sparkfun/SparkFun_Simultaneous_RFID_Reader_M7E/docs/assets/img/Simultaneous-RFID-Reader_M7E-Power.jpg

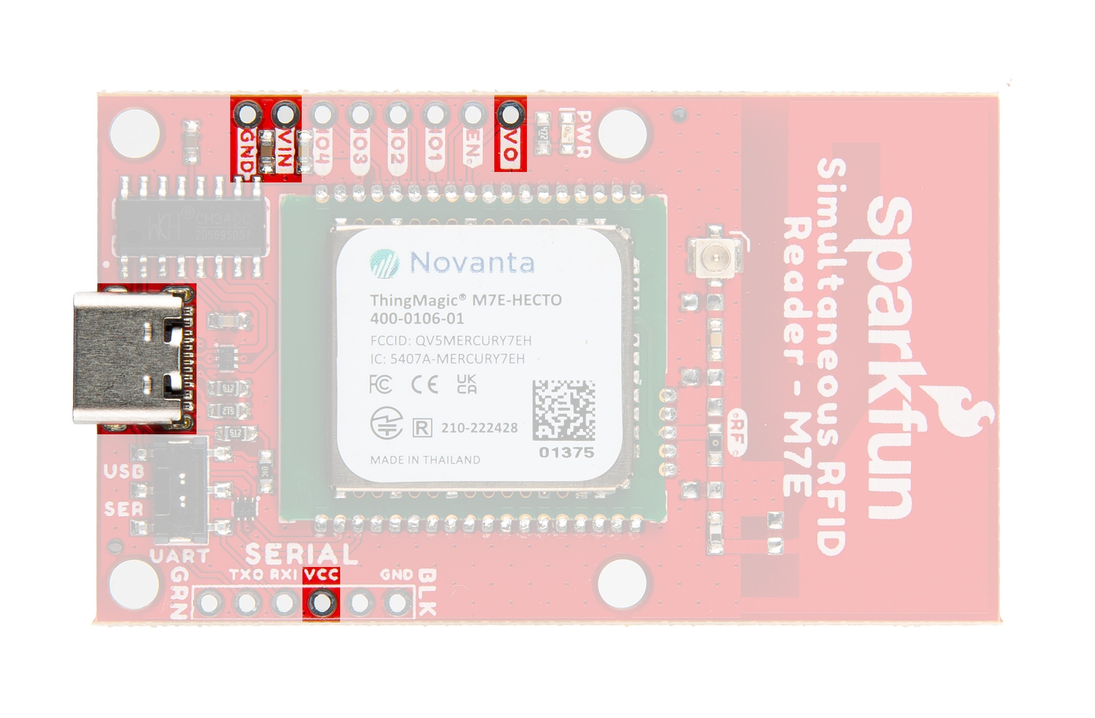
docs/assets/img/Simultaneous-RFID-Reader_M7E-Power.jpg
