sparkfun/SparkFun_Simultaneous_RFID_Reader_M7E/docs/assets/img/Simultaneous-RFID-Reader_M7E-Switch.jpg

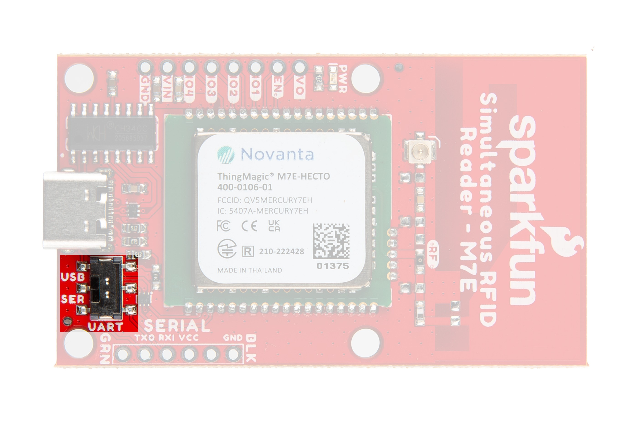
docs/assets/img/Simultaneous-RFID-Reader_M7E-Switch.jpg
