sparkfun/SparkFun_Simultaneous_RFID_Reader_M7E/docs/assets/img/Simultaneous_RFID_Reader_M7E-UFL_to_Antenna_Wire.jpg

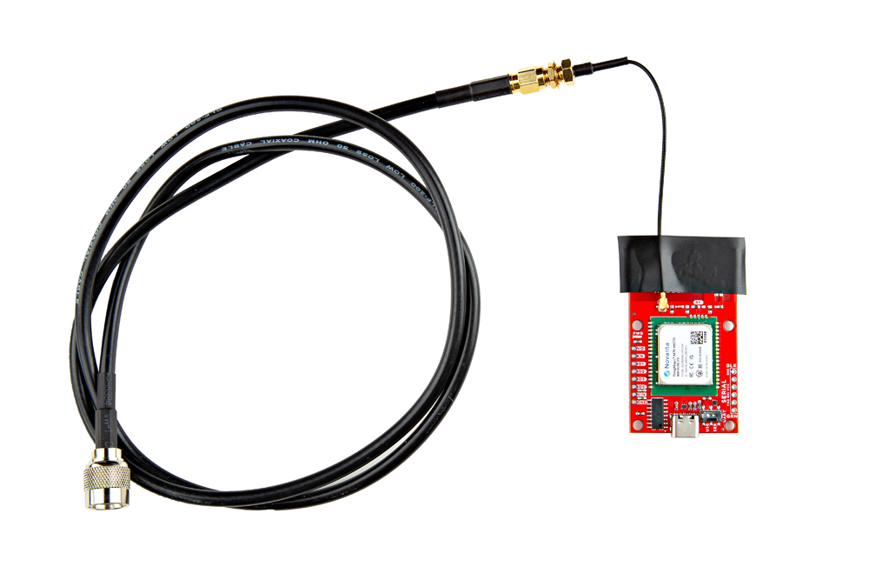
docs/assets/img/Simultaneous_RFID_Reader_M7E-UFL_to_Antenna_Wire.jpg
