sparkfun/SparkFun_Simultaneous_RFID_Reader_M7E/docs/assets/img/URA-M7E_Settings.jpg

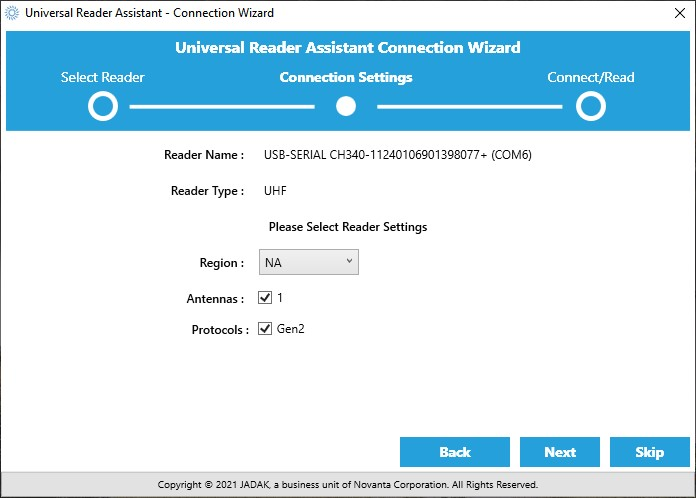
docs/assets/img/URA-M7E_Settings.jpg
