sparkfun/SparkFun_Simultaneous_RFID_Reader_M7E/docs/assets/img/URA-Main_Window.jpg

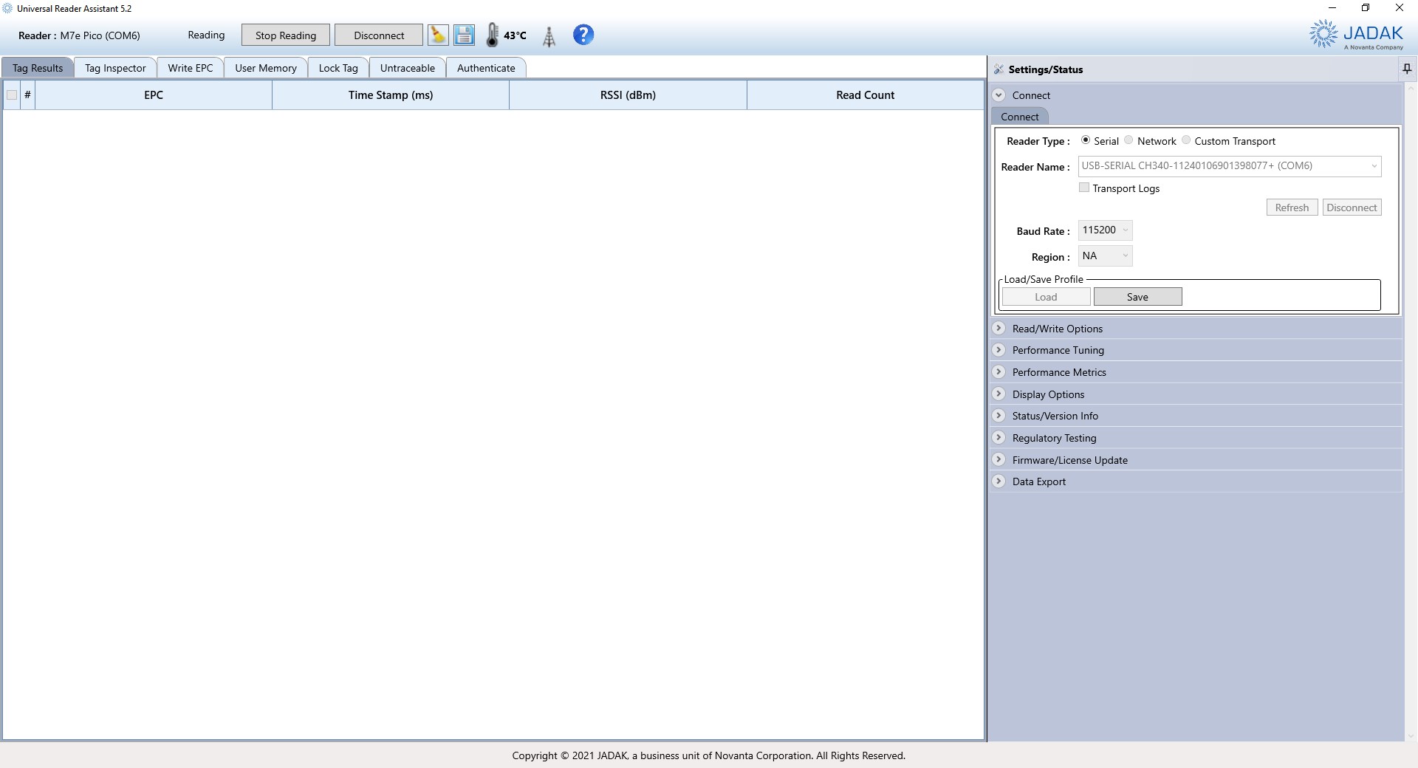
docs/assets/img/URA-Main_Window.jpg
