sparkfun/SparkFun_Simultaneous_RFID_Reader_M7E/docs/assets/img/URA-Read_Write_Options.jpg

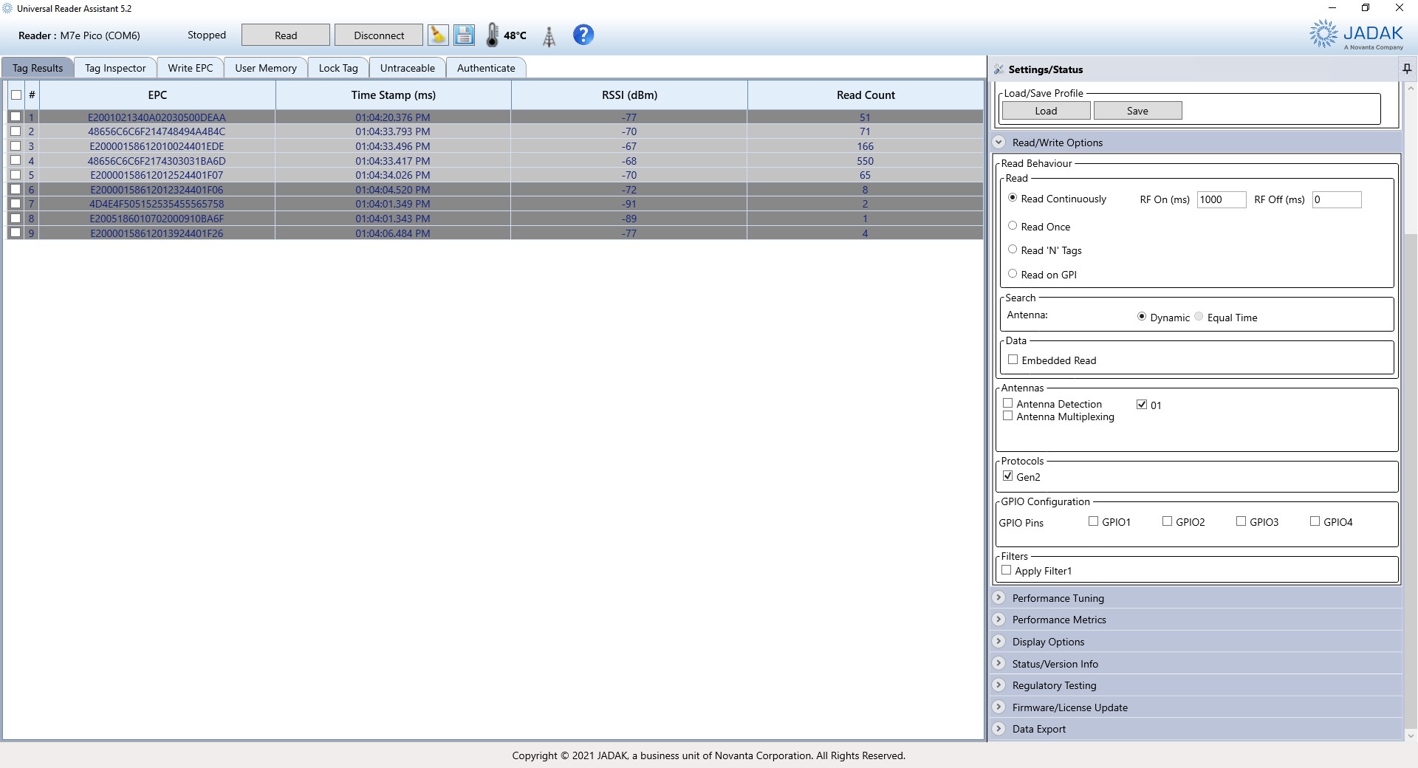
docs/assets/img/URA-Read_Write_Options.jpg
